OffGrid-Devices/Devi/Devi_firmware/Devi_firmware/Devi_firmware/Button.h

/*
* Button.h
*
* Created: 15-04-2018 12:05:15
* Author: tiago
*/


#ifndef __BUTTON_H__
#define __BUTTON_H__

#pragma GCC push_options
#pragma GCC optimize (OPTIMIZATION)

#include "Arduino.h"

class Button
{
	//variables
	public:
	boolean state; // 0-released, 1-pressed
	boolean changed;
	protected:
	private:
	boolean val, _val = 1;

	//functions
	public:
	Button();
	~Button();
	void init(byte p);
	void read();
	//boolean changed();
	protected:
	private:
	Button( const Button &c );
	Button& operator=( const Button &c );
	byte pin;
}; //Button

#pragma GCC pop_options

#endif //__BUTTON_H__
